schnebeck/Sopho2SIP/hardware/gehaeuse/ansichten/gehaeuse_hinten.png

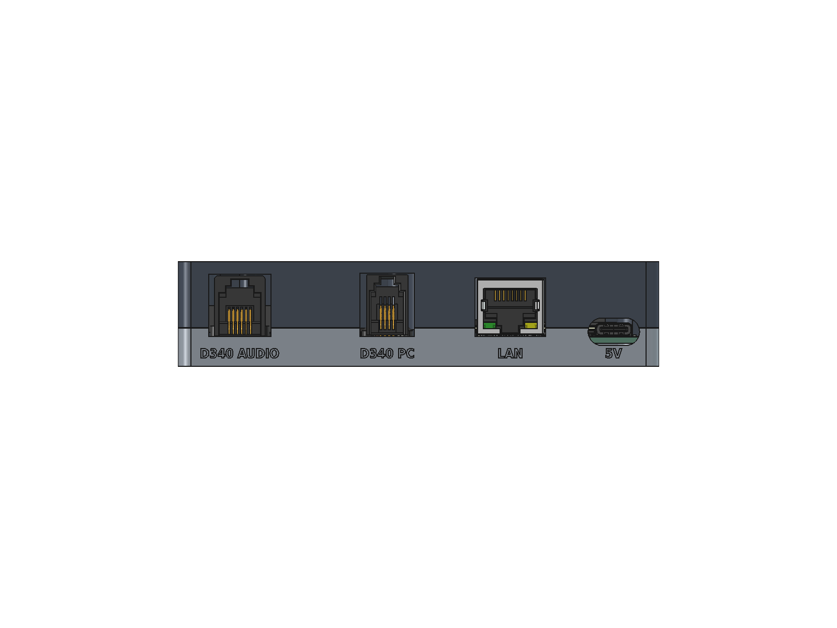
hardware/gehaeuse/ansichten/gehaeuse_hinten.png
