schnebeck/Sopho2SIP/ref/foto_db9_buchse.png

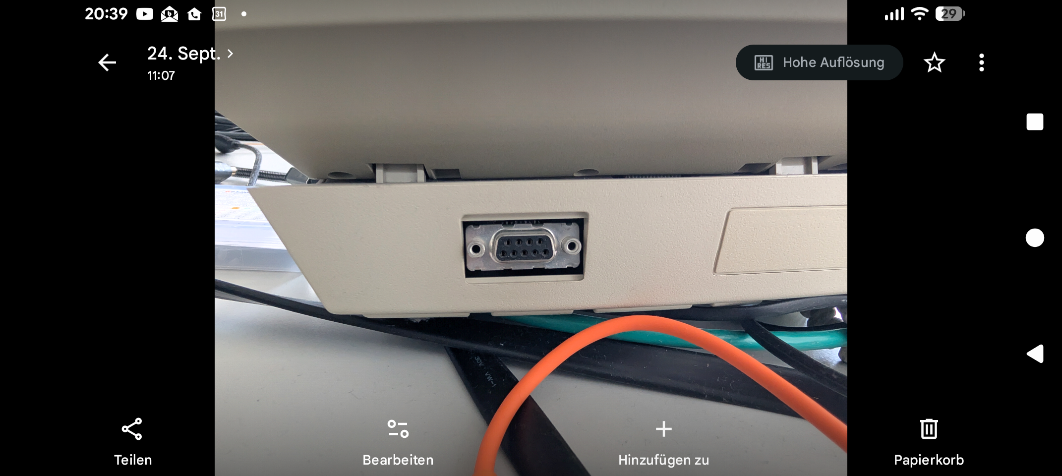
ref/foto_db9_buchse.png
